ceoloide/corney-island/images/backplate-bottom.png

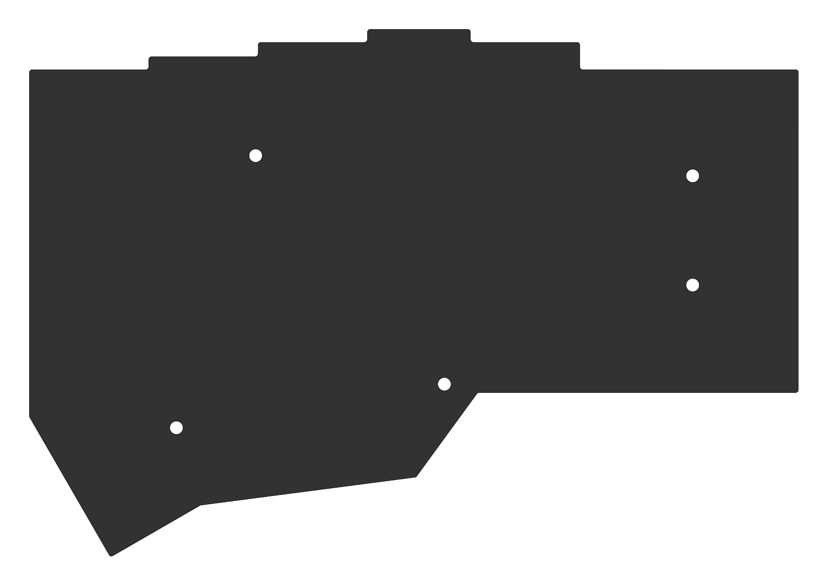
images/backplate-bottom.png
