ceoloide/corney-island/images/backplate-top.png

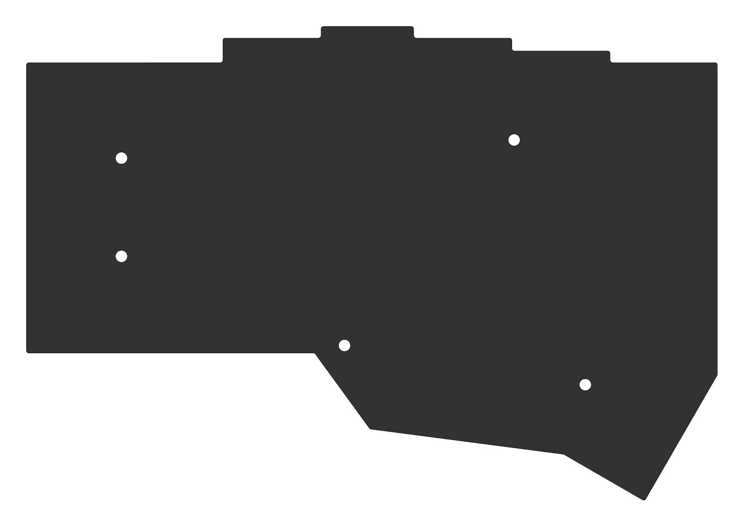
images/backplate-top.png
