ceoloide/corney-island/images/controller_overlay-top.png

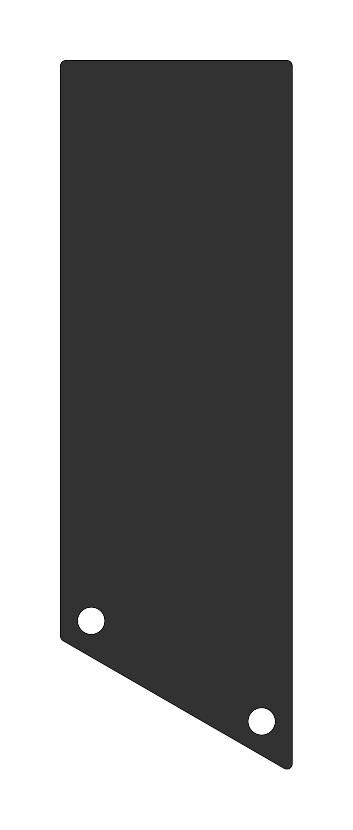
images/controller_overlay-top.png
