ceoloide/corney-island/images/corney_island-top.png

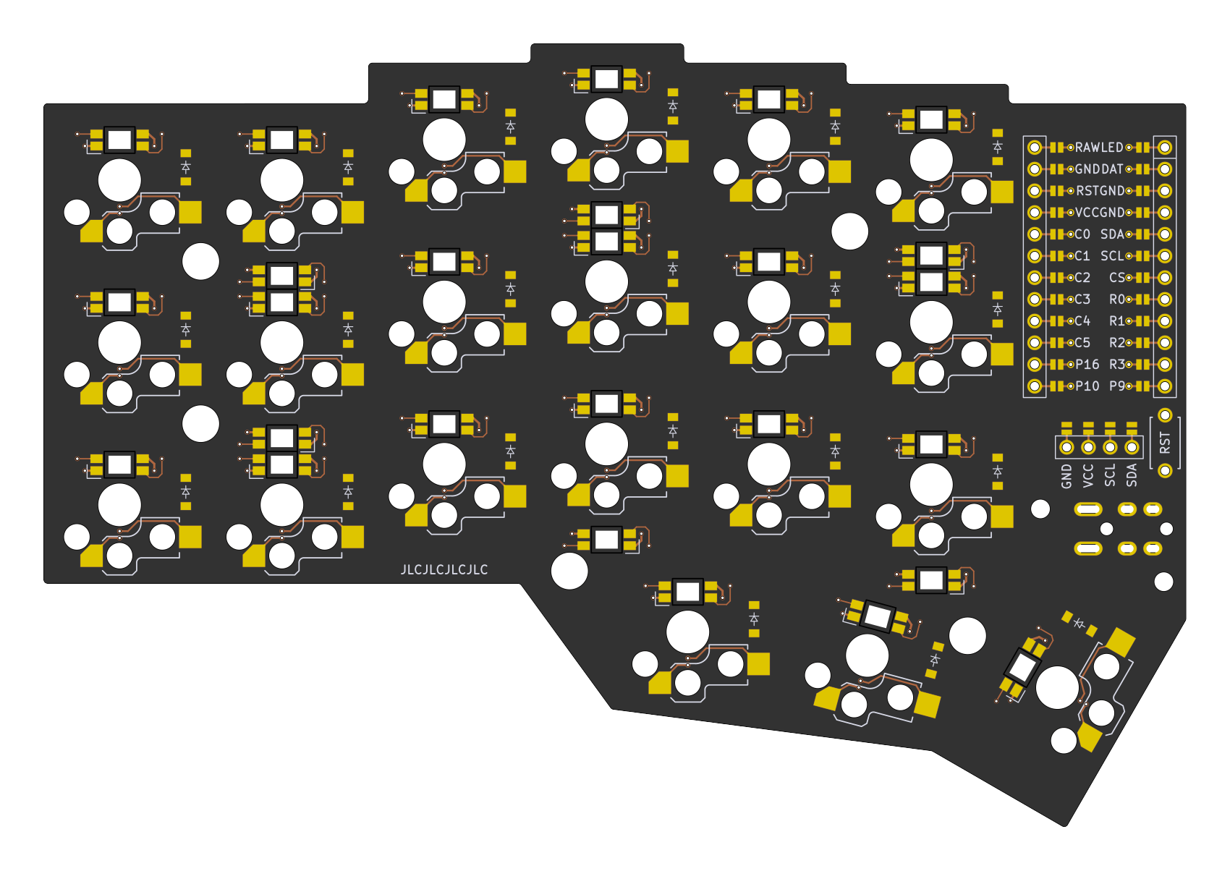
images/corney_island-top.png
