ceoloide/corney-island/images/corney_island_autorouted-bottom.png

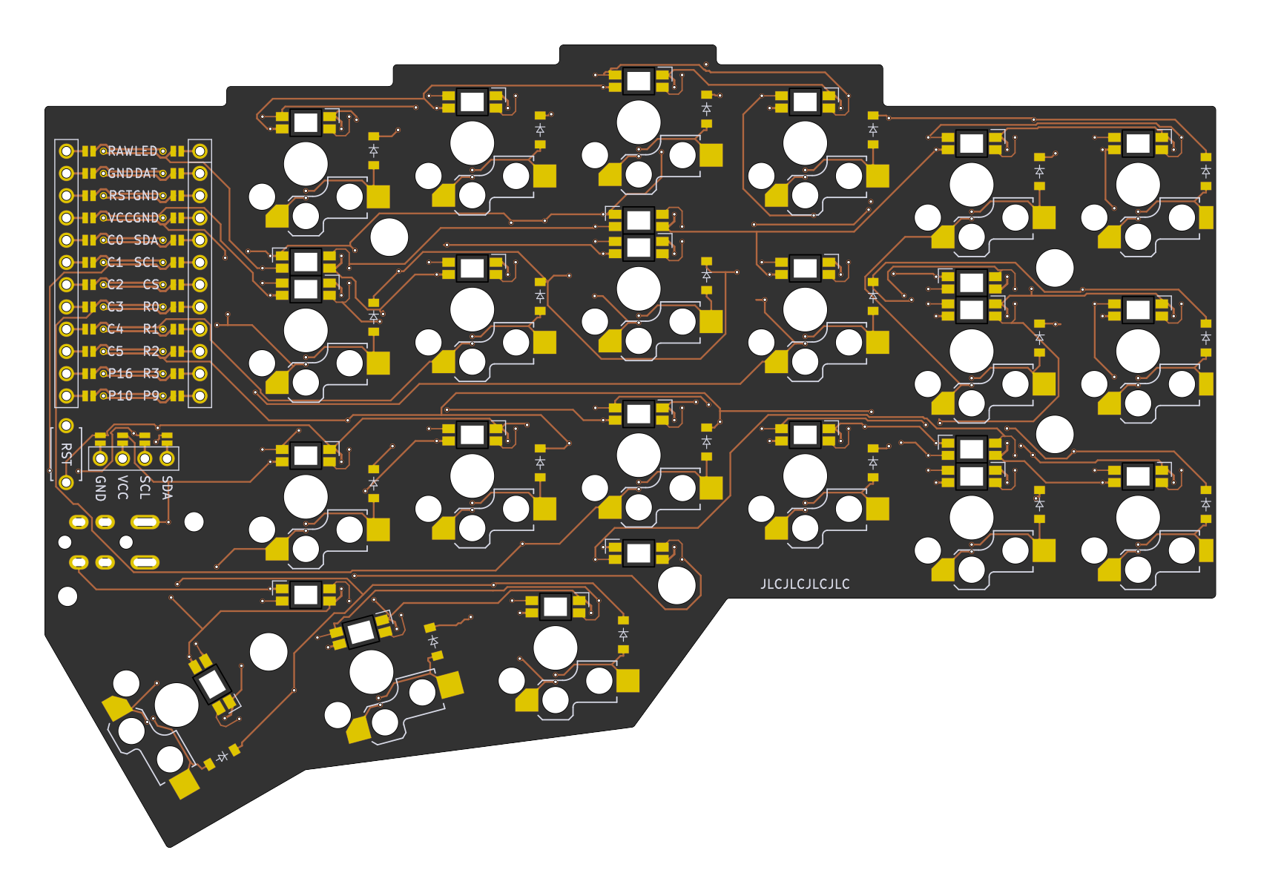
images/corney_island_autorouted-bottom.png
