ceoloide/corney-island/images/corney_island_wireless-top.png

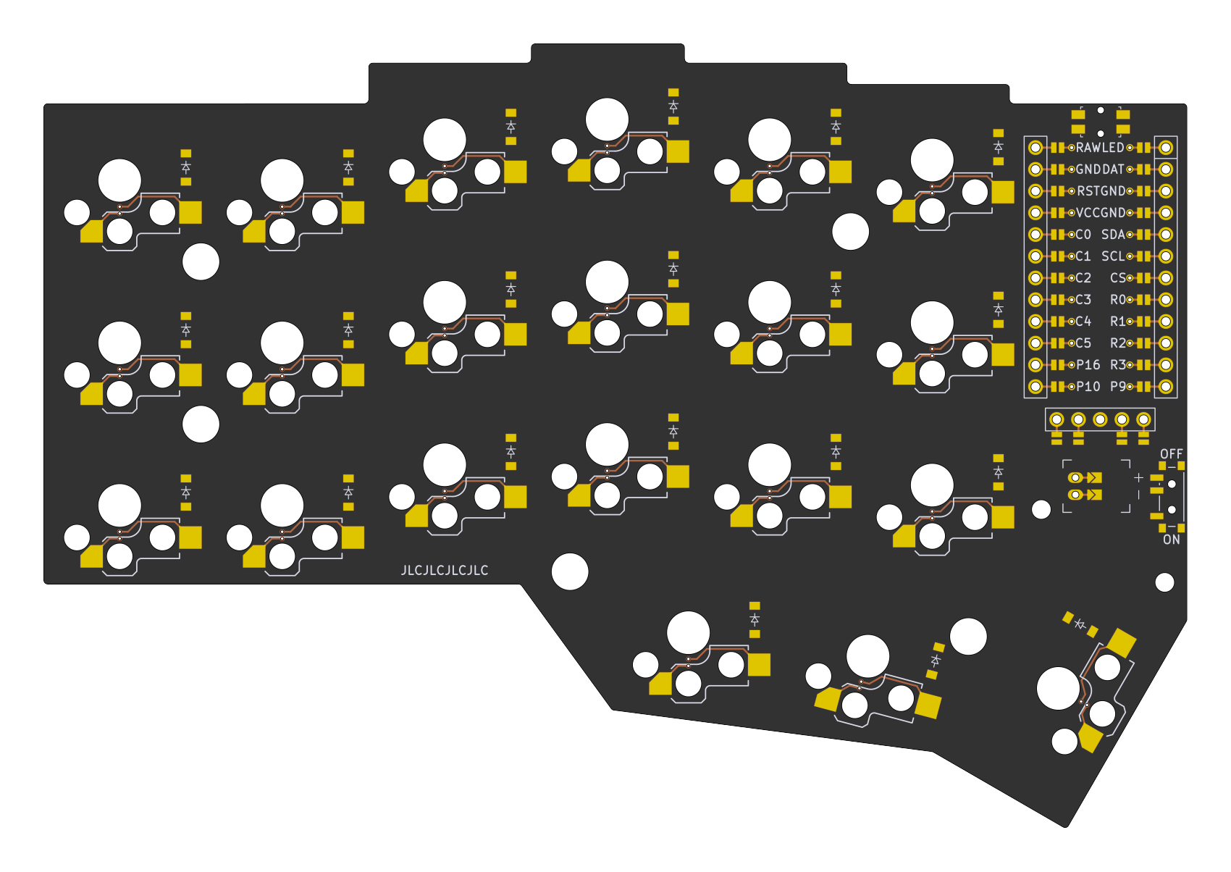
images/corney_island_wireless-top.png
