ceoloide/corney-island/images/frontplate-bottom.png

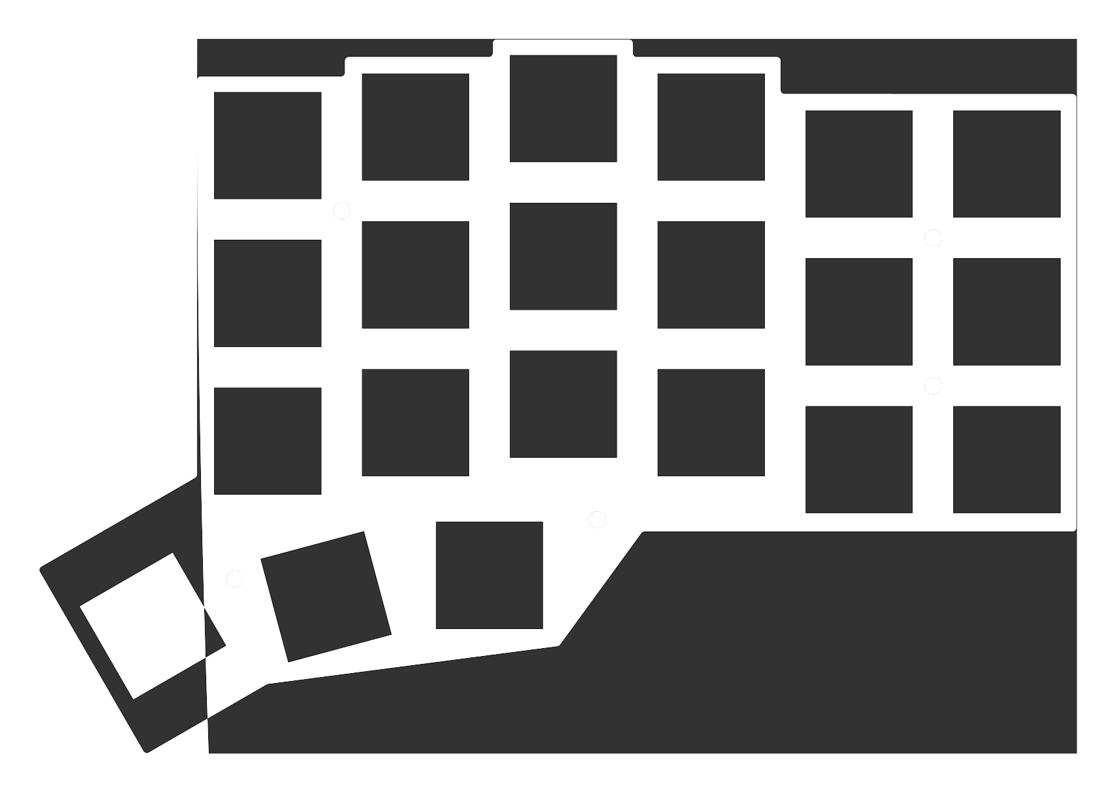
images/frontplate-bottom.png
